gcrcien/STM32_VFO/WhatsApp Image 2023-11-06 at 07.51.49.jpeg

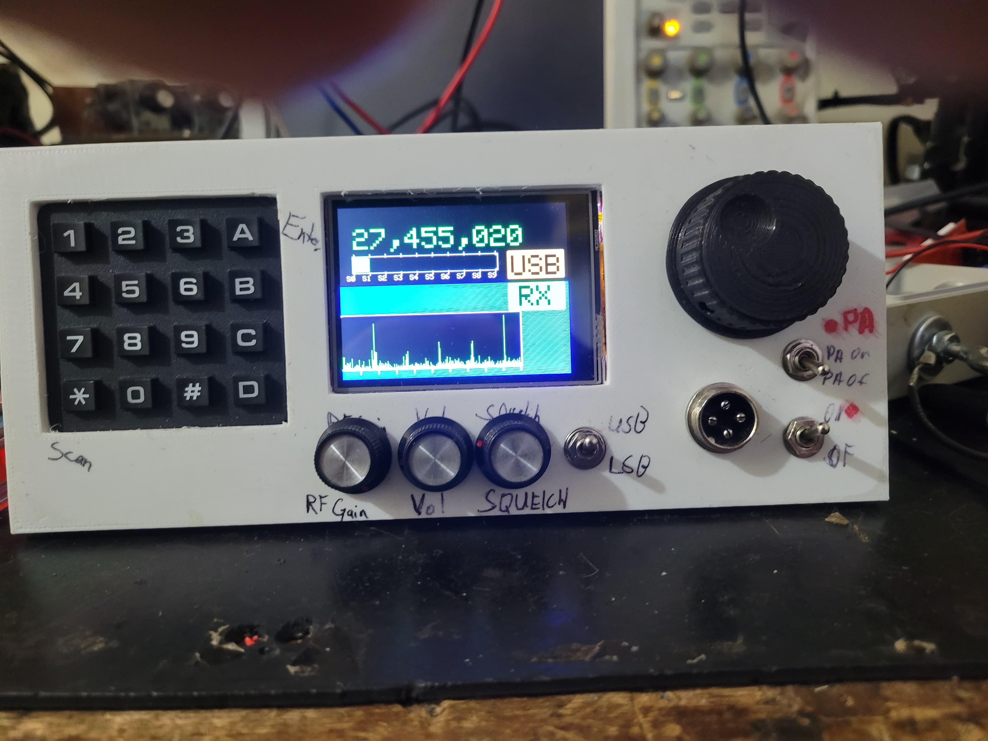
WhatsApp Image 2023-11-06 at 07.51.49.jpeg
